mathieupommery/YOLO_N6/DOC/cerf.png

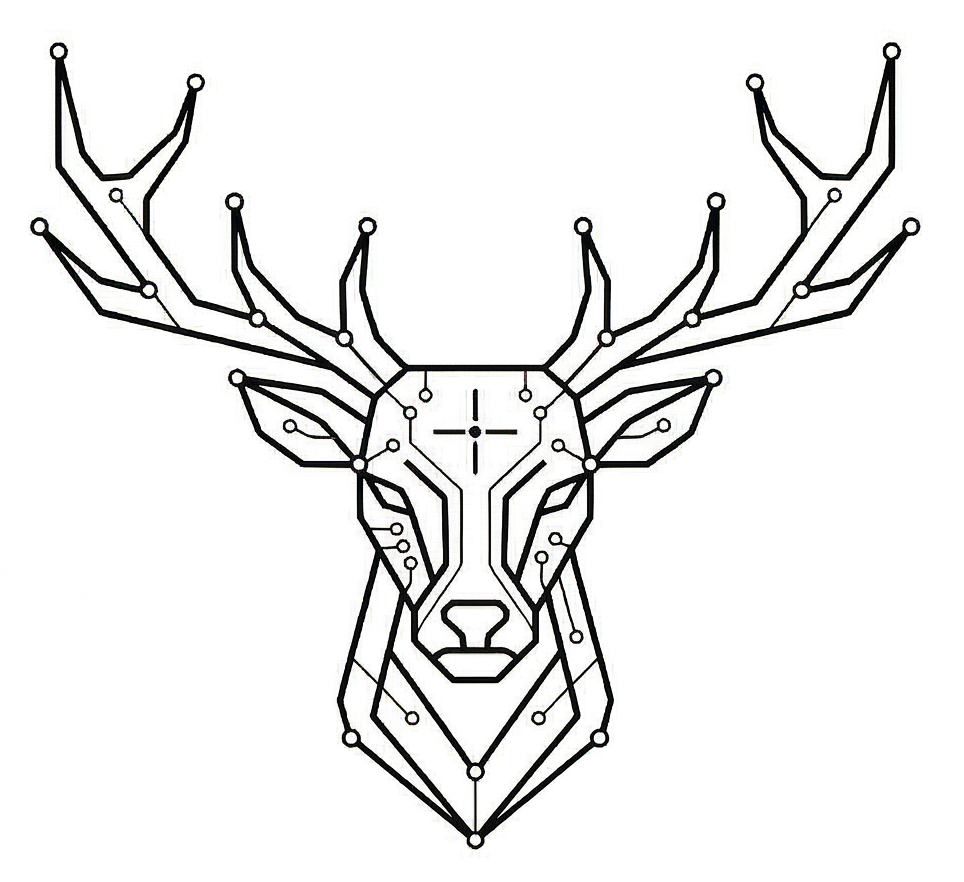
DOC/cerf.png
