mathieupommery/YOLO_N6/DOC/l1.png

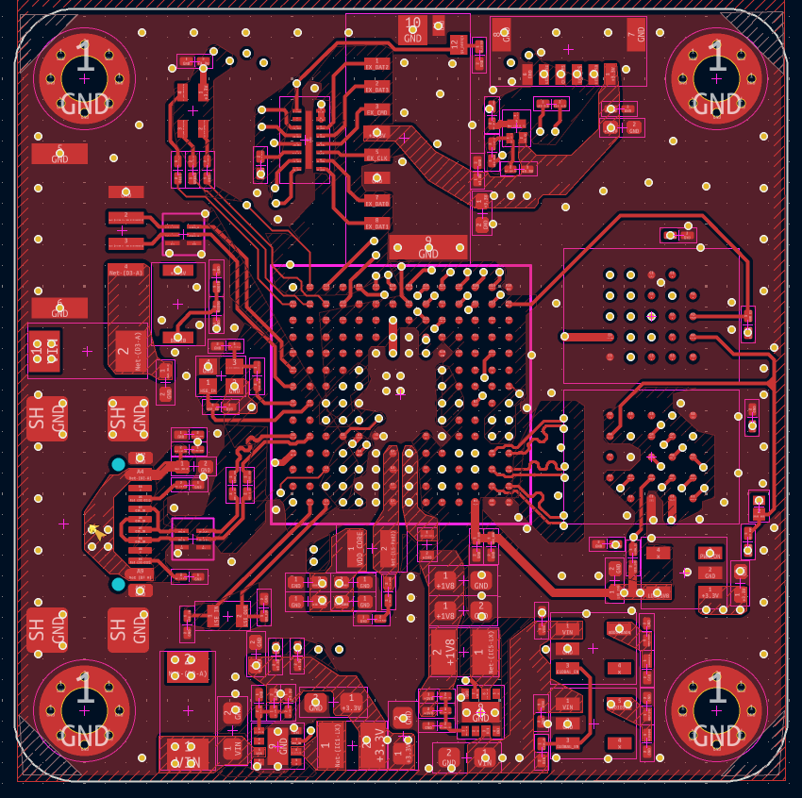
DOC/l1.png
