mathieupommery/YOLO_N6/DOC/l3.png

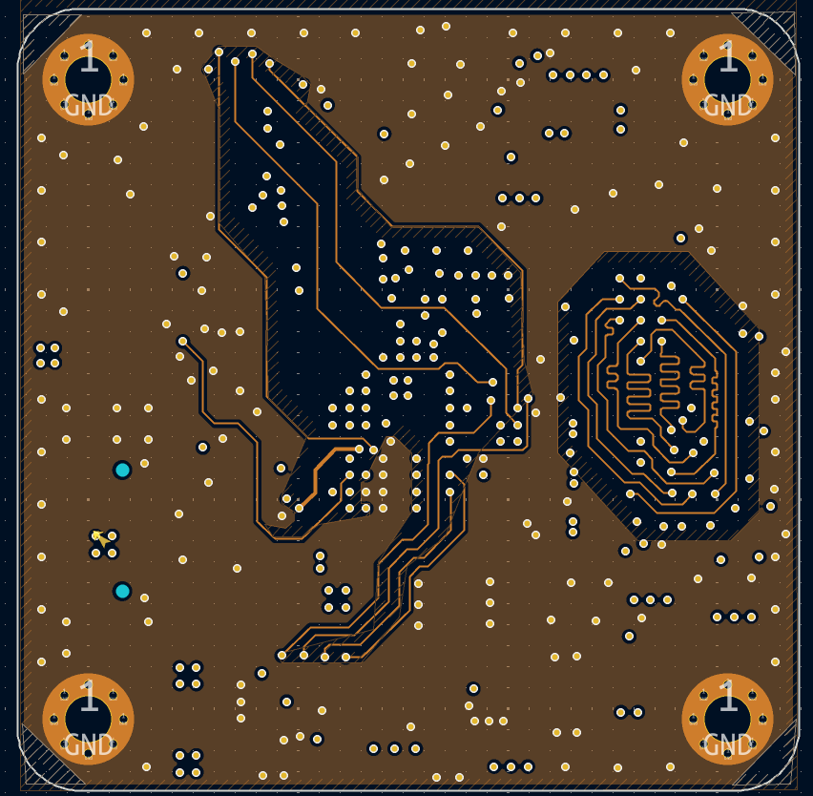
DOC/l3.png
