mathieupommery/YOLO_N6/DOC/l4.png

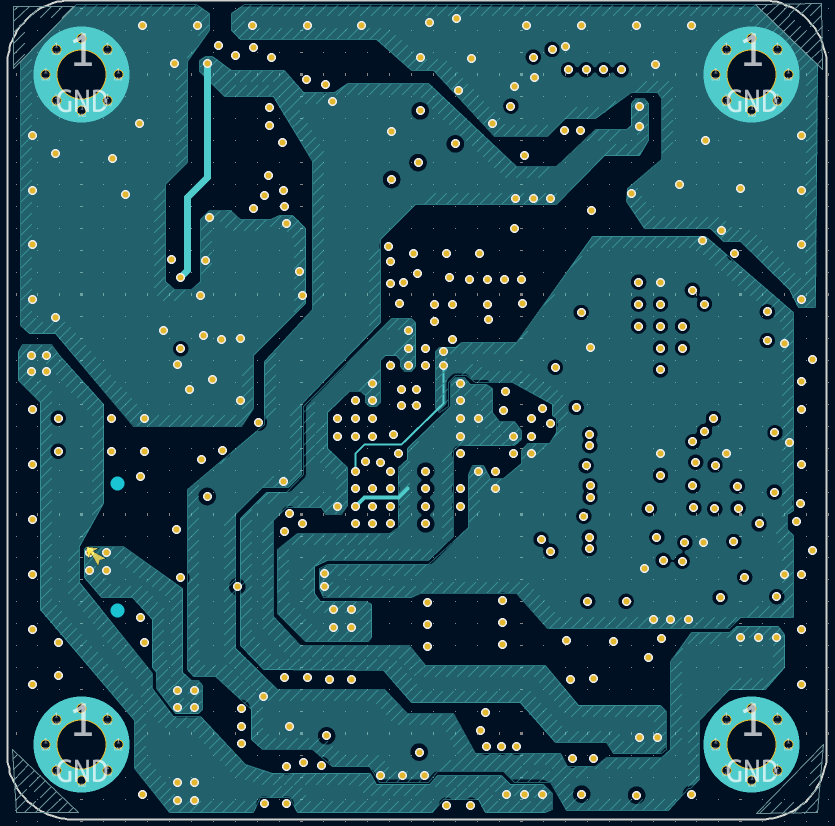
DOC/l4.png
