mathieupommery/YOLO_N6/DOC/l5.png

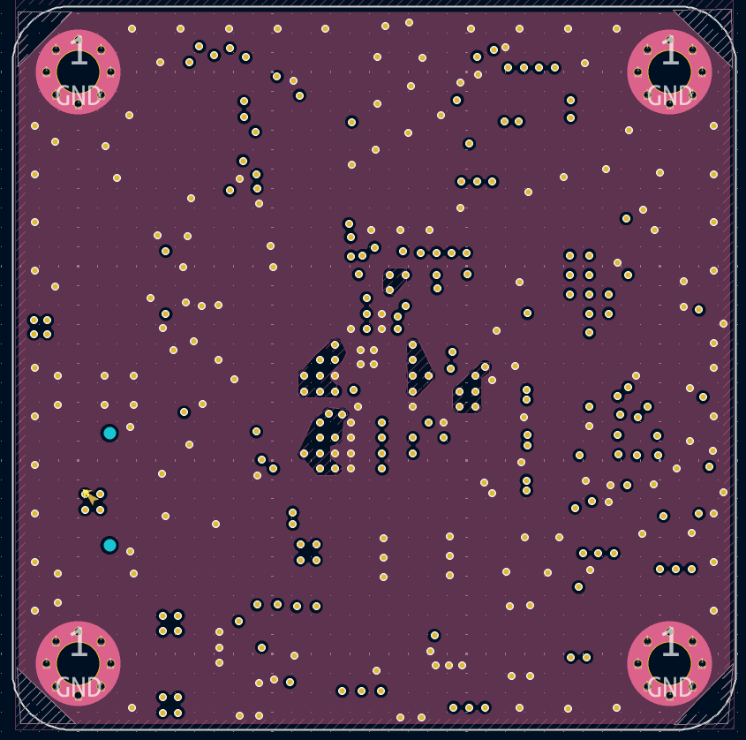
DOC/l5.png
