mathieupommery/YOLO_N6/DOC/l6.png

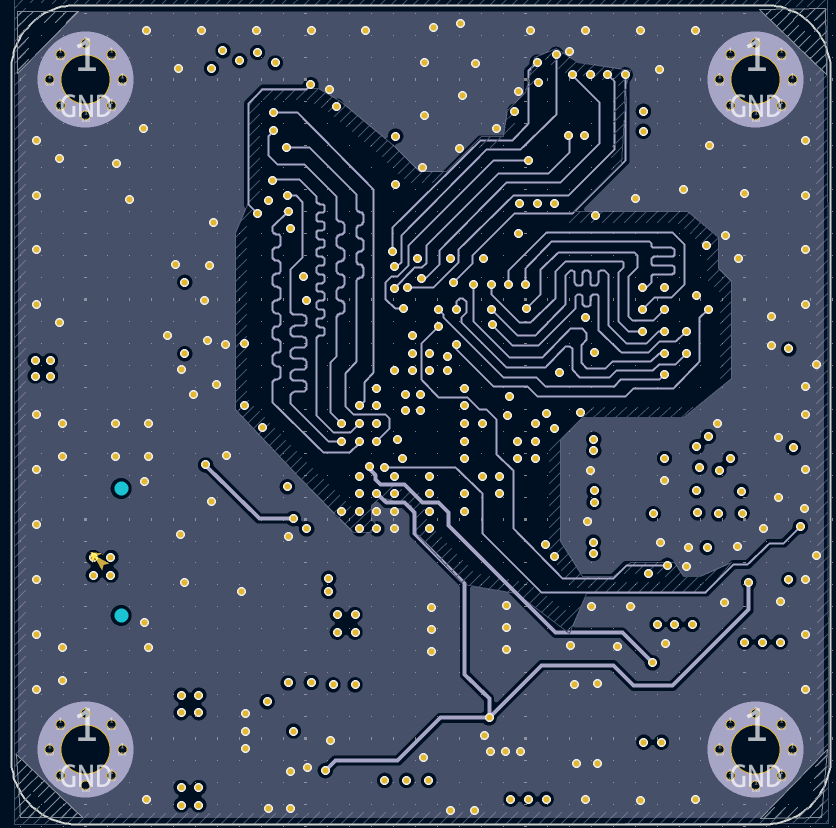
DOC/l6.png
