mathieupommery/YOLO_N6/DOC/memory.png

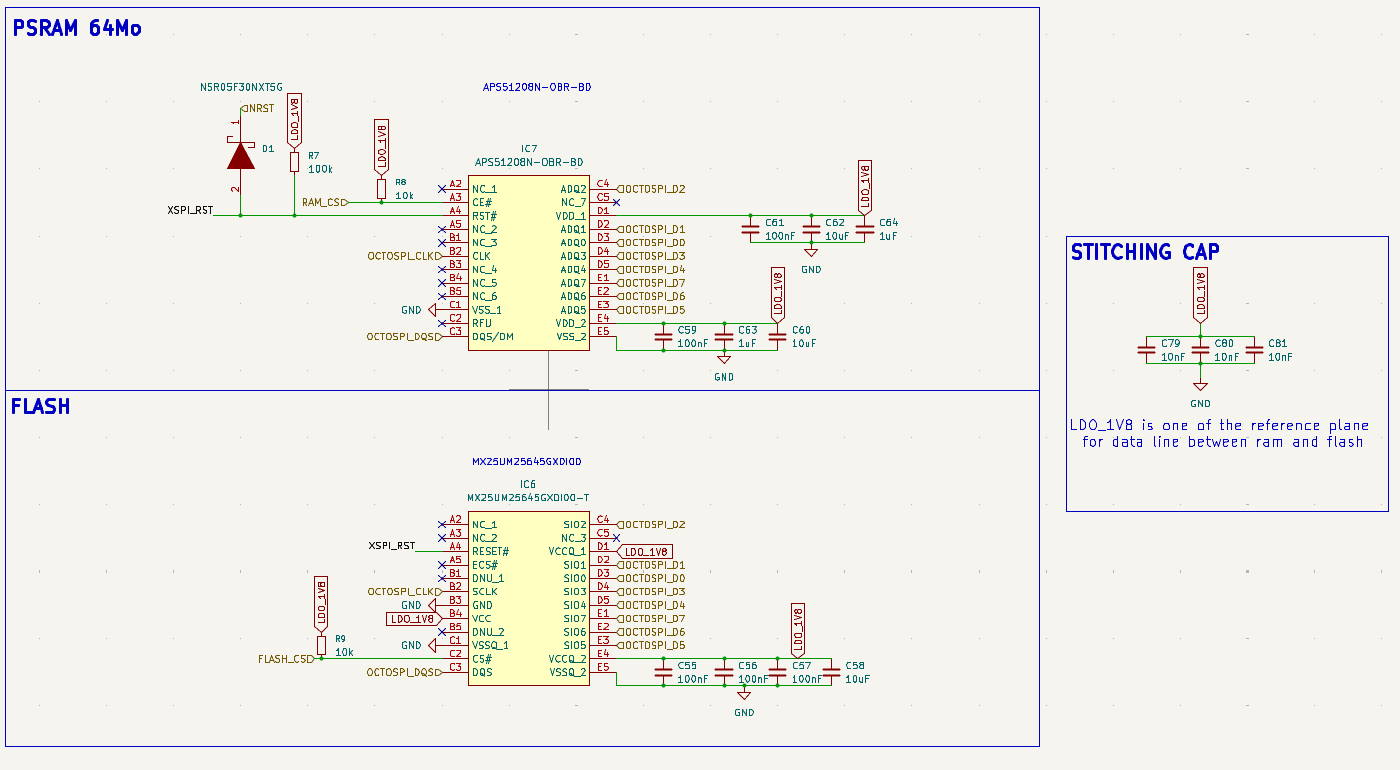
DOC/memory.png
