mathieupommery/YOLO_N6/DOC/power.png

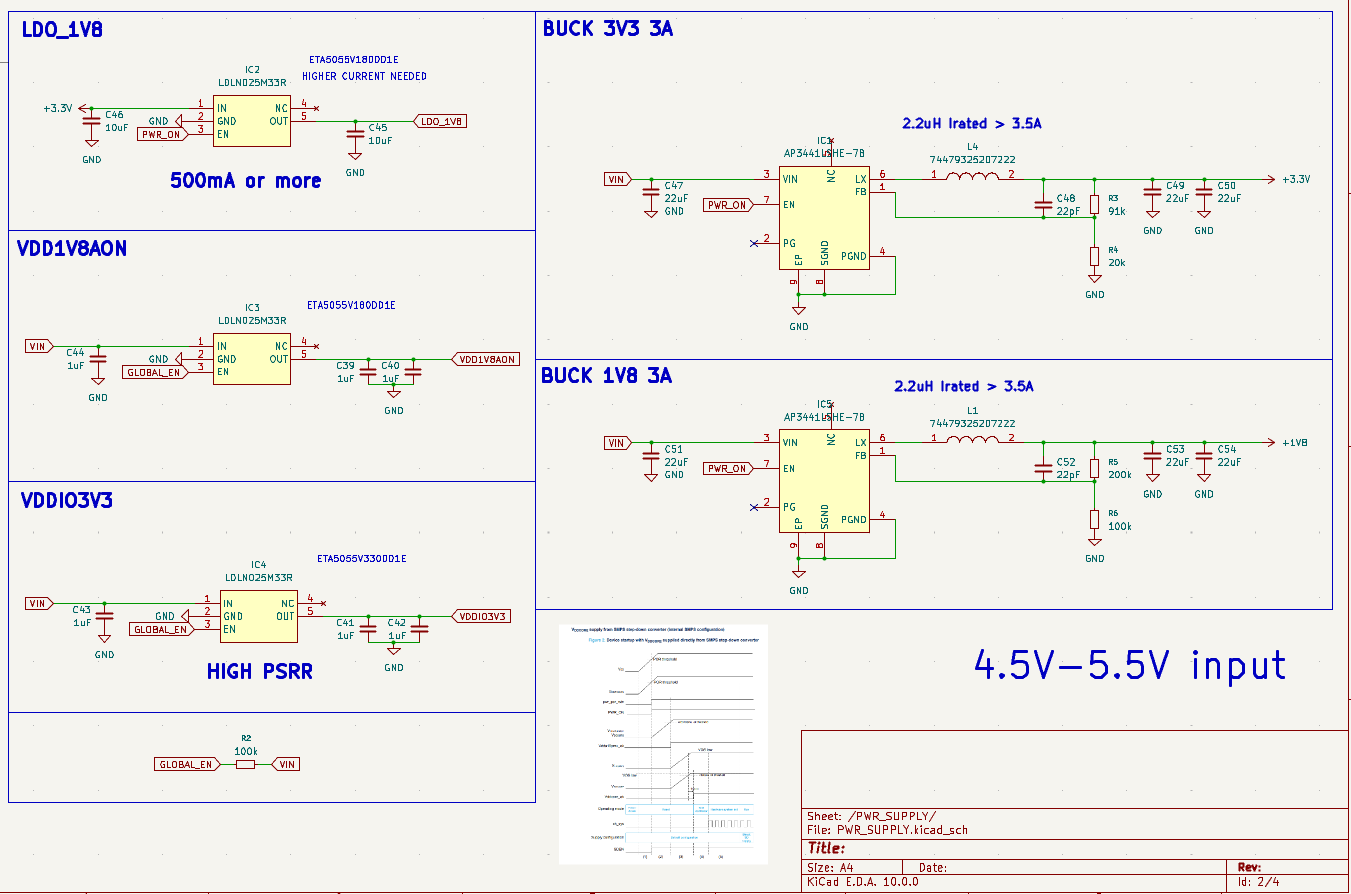
DOC/power.png
